MikolajDIY/ForZero/Oprogramowanie sterownika/ForZero_kod_STM_1v1/Core/Inc/CAN_motor.h

/*
 * CAN_motor.h
 *
 *  Created on: 12 sie 2026
 *      Author: rataj
 */

#ifndef INC_CAN_MOTOR_H_
#define INC_CAN_MOTOR_H_

#include "main.h"
#include <stdbool.h>

void Send_RPM(uint16_t rpm);

// void Send_Fuel_Consumption_RB4(uint8_t rate); // FAIL

#endif /* INC_CAN_MOTOR_H_ */
