MikolajDIY/ForZero/Oprogramowanie sterownika/ForZero_kod_STM_1v1/Core/Src/fuel_and_temp.c

/*
 * fuel_and_temp.c
 *
 *  Created on: 14 sie 2026
 *      Author: rataj
 */
#include "main.h"
#include "mcp4661.h"

extern I2C_HandleTypeDef hi2c1;

//-------------- FUEL LUT------------------------
static const uint8_t fuel_raw_lut[101] = {
	44,  44,  44,  45,  45,  46,  46,  46,  47,  47, //  0% - 9%
	47,  48,  48,  49,  49,  50,  50,  51,  51,  52, // 10% - 19%
	52,  53,  53,  54,  54,  55,  55,  56,  56,  57, // 20% - 29%
	58,  58,  59,  59,  60,  61,  61,  62,  62,  63, // 30% - 39%
	63,  64,  65,  65,  66,  67,  67,  68,  68,  69, // 40% - 49%
	69,  70,  70,  71,  72,  72,  73,  74,  74,  75, // 50% - 59%
	75,  76,  76,  77,  77,  78,  78,  79,  80,  80, // 60% - 69%
	81,  81,  82,  82,  83,  83,  84,  84,  85,  85, // 70% - 79%
	86,  86,  87,  87,  88,  88,  89,  89,  89,  90, // 80% - 89%
	90,  90,  91,  91,  91,  91,  92,  92,  92,  92, // 90% - 99%
	92                                      // 100%
};
//-----------------------------------------------

//-------------------TEMP LUT -----------------------------------
static const uint8_t temp_raw_lut[101] = {
		33, 34, 35, 36, 37, 37, 38, 39, 40, 41, //  0% - 9%
		42, 42, 43, 44, 45, 46, 46, 47, 48, 49, // 10% - 19%
		50, 50, 51, 52, 52, 53, 53, 54, 54, 55, // 20% - 29%
		55, 56, 56, 56, 57, 57, 57, 58, 58, 58, // 30% - 39%
		59, 59, 59, 59, 59, 60, 60, 61, 61, 62, // 40% - 49%
		63, 99, 100, 100, 100, 101, 101, 101, 101, 101, // 50% - 59%
		101, 102, 102, 102, 102, 103, 103, 103, 103, 104, // 60% - 69%
		104, 104, 104, 105, 105, 105, 105, 105, 106, 106, // 70% - 79%
		106, 106, 107, 107, 107, 107, 107, 108, 108, 108, // 80% - 89%
		109, 109, 109, 110, 110, 110, 111, 111, 111, 112, // 90% - 99%
		112                                                // 100%
};
//-------------------------------------------------------------------

void Send_Engine_Temperature(uint8_t temp_lvl_pct){

	if (temp_lvl_pct > 100) {
		temp_lvl_pct = 100;
	}

	uint8_t temp_lvl_raw = temp_raw_lut[temp_lvl_pct];

	if (hi2c1.State != HAL_I2C_STATE_READY) {
	        HAL_I2C_DeInit(&hi2c1);
	        HAL_I2C_Init(&hi2c1);
	}

	MCP4661_SetWiper(&hi2c1, MCP4661_VOLATILE_WIPER_0, temp_lvl_raw);
}

void Send_Fuel_lvl(uint8_t fuel_lvl_pct){

	if (fuel_lvl_pct > 100) {
		fuel_lvl_pct = 100;
	}

	uint8_t fuel_lvl_raw = fuel_raw_lut[fuel_lvl_pct];

	if (hi2c1.State != HAL_I2C_STATE_READY) {
	        HAL_I2C_DeInit(&hi2c1);
	        HAL_I2C_Init(&hi2c1);
	}

	MCP4661_SetWiper(&hi2c1, MCP4661_VOLATILE_WIPER_1, fuel_lvl_raw);
}
